TinyCircuits/TinyCircuits-TinyShield-WiFi-ATWINC1500-ASD2123/images/ASD2123-R-Tutorial-Image-03.jpg

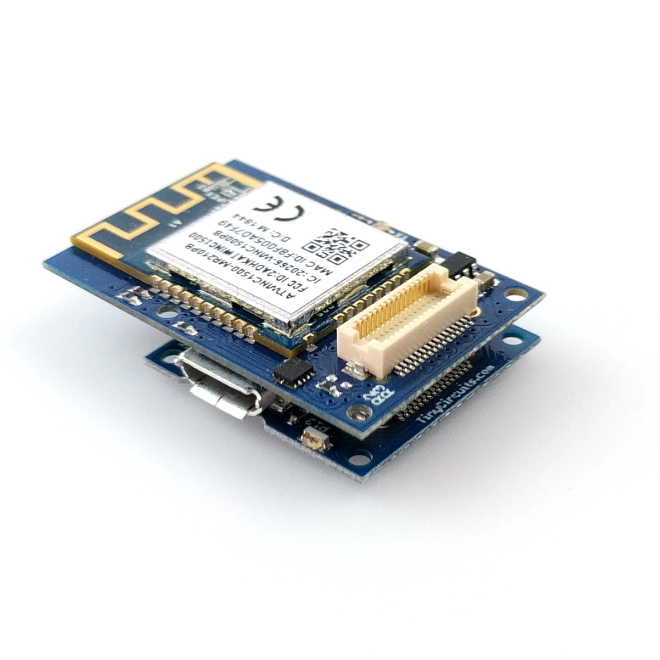
images/ASD2123-R-Tutorial-Image-03.jpg
